ccmpbll/bitclock-redux/bitclock-fw/main/tasks/wifi_ap.c

#include "wifi_ap.h"

#include "esp_http_server.h"
#include "esp_log.h"
#include "esp_wifi.h"
#include "freertos/FreeRTOS.h"
#include "freertos/event_groups.h"
#include "tasks/wifi.h"
#include <string.h>

static const char *TAG = "wifi_ap";

#define AP_SSID "bitclock-setup"
#define AP_MAX_CONNECTIONS 4

static httpd_handle_t http_server = NULL;

// Minimal URI-decode: decodes %XX and converts + to space, in-place.
static void uri_decode(char *dst, const char *src, size_t dst_len) {
  size_t di = 0;
  for (size_t si = 0; src[si] && di + 1 < dst_len; si++) {
    if (src[si] == '%' && src[si + 1] && src[si + 2]) {
      char hex[3] = {src[si + 1], src[si + 2], '\0'};
      dst[di++] = (char)strtol(hex, NULL, 16);
      si += 2;
    } else if (src[si] == '+') {
      dst[di++] = ' ';
    } else {
      dst[di++] = src[si];
    }
  }
  dst[di] = '\0';
}

static const char *SETUP_PAGE_TEMPLATE =
    "<!DOCTYPE html>"
    "<html lang='en'>"
    "<head>"
    "<meta charset='UTF-8'>"
    "<meta name='viewport' content='width=device-width,initial-scale=1'>"
    "<title>Bitclock Wi-Fi Setup</title>"
    "<style>"
    "body{margin:0;padding:24px 16px;background:rgb(245,242,240);"
    "color:rgb(41,41,41);font-family:-apple-system,BlinkMacSystemFont,"
    "'Segoe UI',Roboto,Helvetica,Arial,sans-serif;}"
    "h1{font-size:1.4rem;font-weight:700;margin:0 0 4px;}"
    "p.sub{margin:0 0 24px;color:rgb(130,120,110);font-size:.9rem;}"
    ".card{background:#fff;border-radius:8px;padding:20px;"
    "max-width:400px;box-shadow:0 1px 4px rgba(0,0,0,.08);}"
    "label{display:block;font-size:.85rem;font-weight:600;margin-bottom:4px;}"
    "select,input{width:100%;box-sizing:border-box;padding:8px 10px;"
    "border:1px solid rgb(200,195,190);border-radius:6px;"
    "font-size:.95rem;background:#fff;color:rgb(41,41,41);margin-bottom:16px;}"
    "button{width:100%;padding:10px;border:none;border-radius:6px;"
    "background:linear-gradient(217deg,#4c6ef5,#22b8cf);"
    "color:#fff;font-size:1rem;font-weight:600;cursor:pointer;}"
    "button:active{opacity:.85;}"
    ".err{color:#c0392b;font-size:.85rem;margin-bottom:12px;display:none;}"
    "</style>"
    "</head>"
    "<body>"
    "<h1>Bitclock Wi-Fi Setup</h1>"
    "<p class='sub'>%s</p>"
    "<div class='card'>"
    "<form method='POST' action='/connect' id='f'>"
    "<label for='ssid'>Network</label>"
    "<select name='ssid' id='ssid'>%s</select>"
    "<label for='pw'>Password</label>"
    "<input type='password' name='password' id='pw' autocomplete='current-password'>"
    "<p class='err' id='err'>Please select a network.</p>"
    "<button type='submit'>Connect</button>"
    "</form>"
    "</div>"
    "<script>"
    "document.getElementById('f').onsubmit=function(){"
    "if(!document.getElementById('ssid').value){"
    "document.getElementById('err').style.display='block';return false;}"
    "return true;};"
    "</script>"
    "</body>"
    "</html>";

static const char *SUCCESS_PAGE =
    "<!DOCTYPE html>"
    "<html lang='en'>"
    "<head>"
    "<meta charset='UTF-8'>"
    "<meta name='viewport' content='width=device-width,initial-scale=1'>"
    "<title>Bitclock</title>"
    "<style>"
    "body{margin:0;padding:24px 16px;background:rgb(245,242,240);"
    "color:rgb(41,41,41);font-family:-apple-system,BlinkMacSystemFont,"
    "'Segoe UI',Roboto,Helvetica,Arial,sans-serif;text-align:center;}"
    "h1{font-size:1.4rem;font-weight:700;margin:48px 0 8px;}"
    "p{color:rgb(130,120,110);font-size:.95rem;}"
    "</style>"
    "</head>"
    "<body>"
    "<h1>Credentials saved.</h1>"
    "<p>Bitclock is restarting and will connect to your network.</p>"
    "<p>You can close this page.</p>"
    "</body>"
    "</html>";

static esp_err_t get_handler(httpd_req_t *req) {
  wifi_scan_config_t scan_cfg = {
      .ssid = NULL,
      .bssid = NULL,
      .channel = 0,
      .show_hidden = false,
  };

  esp_wifi_scan_start(&scan_cfg, true); // blocking scan

  uint16_t ap_count = 0;
  esp_wifi_scan_get_ap_num(&ap_count);
  if (ap_count > 20) {
    ap_count = 20;
  }

  wifi_ap_record_t *ap_records =
      (wifi_ap_record_t *)malloc(ap_count * sizeof(wifi_ap_record_t));
  if (!ap_records) {
    httpd_resp_send_500(req);
    return ESP_FAIL;
  }
  esp_wifi_scan_get_ap_records(&ap_count, ap_records);

  // Build <option> list — each entry: template(~27 bytes) + 2x SSID (max 32 bytes each)
  size_t opts_size = ap_count * 96 + 64;
  char *opts = (char *)malloc(opts_size);
  if (!opts) {
    free(ap_records);
    httpd_resp_send_500(req);
    return ESP_FAIL;
  }
  opts[0] = '\0';
  strlcat(opts, "<option value=''>Select a network...</option>", opts_size);
  for (uint16_t i = 0; i < ap_count; i++) {
    char opt[96];
    snprintf(opt, sizeof(opt), "<option value='%s'>%s</option>",
             (char *)ap_records[i].ssid, (char *)ap_records[i].ssid);
    strlcat(opts, opt, opts_size);
  }
  free(ap_records);

  const char *subtitle = (bool)req->user_ctx
                             ? "Could not connect to saved network."
                             : "Connect your Bitclock to Wi-Fi.";

  size_t page_size = strlen(SETUP_PAGE_TEMPLATE) + strlen(subtitle) +
                     strlen(opts) + 32;
  char *page = (char *)malloc(page_size);
  if (!page) {
    free(opts);
    httpd_resp_send_500(req);
    return ESP_FAIL;
  }
  snprintf(page, page_size, SETUP_PAGE_TEMPLATE, subtitle, opts);
  free(opts);

  httpd_resp_set_type(req, "text/html");
  httpd_resp_send(req, page, HTTPD_RESP_USE_STRLEN);
  free(page);
  return ESP_OK;
}

static esp_err_t post_handler(httpd_req_t *req) {
  char body[200] = {0};
  int received = httpd_req_recv(req, body, sizeof(body) - 1);
  if (received <= 0) {
    httpd_resp_send_500(req);
    return ESP_FAIL;
  }
  body[received] = '\0';

  // Parse ssid=...&password=...
  char raw_ssid[64] = {0};
  char raw_password[128] = {0};

  char *ssid_start = strstr(body, "ssid=");
  if (ssid_start) {
    ssid_start += 5;
    char *end = strchr(ssid_start, '&');
    size_t len = end ? (size_t)(end - ssid_start) : strlen(ssid_start);
    if (len >= sizeof(raw_ssid))
      len = sizeof(raw_ssid) - 1;
    strncpy(raw_ssid, ssid_start, len);
    raw_ssid[len] = '\0';
  }

  char *pw_start = strstr(body, "password=");
  if (pw_start) {
    pw_start += 9;
    char *end = strchr(pw_start, '&');
    size_t len = end ? (size_t)(end - pw_start) : strlen(pw_start);
    if (len >= sizeof(raw_password))
      len = sizeof(raw_password) - 1;
    strncpy(raw_password, pw_start, len);
    raw_password[len] = '\0';
  }

  char ssid[32] = {0};
  char password[64] = {0};
  uri_decode(ssid, raw_ssid, sizeof(ssid));
  uri_decode(password, raw_password, sizeof(password));

  if (ssid[0] == '\0') {
    httpd_resp_set_status(req, "400 Bad Request");
    httpd_resp_send(req, "Missing SSID", HTTPD_RESP_USE_STRLEN);
    return ESP_FAIL;
  }

  ESP_LOGI(TAG, "Received credentials for SSID: %s", ssid);

  // Save credentials via the standard wifi path so they persist across reboot
  wifi_config_t wifi_cfg = {0};
  strncpy((char *)wifi_cfg.sta.ssid, ssid, sizeof(wifi_cfg.sta.ssid));
  strncpy((char *)wifi_cfg.sta.password, password,
          sizeof(wifi_cfg.sta.password));
  esp_wifi_set_config(WIFI_IF_STA, &wifi_cfg);

  httpd_resp_set_type(req, "text/html");
  httpd_resp_send(req, SUCCESS_PAGE, HTTPD_RESP_USE_STRLEN);

  vTaskDelay(pdMS_TO_TICKS(500)); // Let the response flush
  esp_restart();

  return ESP_OK;
}

void wifi_ap_start(bool is_fallback) {
  ESP_LOGI(TAG, "Starting AP mode (fallback=%d)", is_fallback);

  // Switch to APSTA so we can still run a WiFi scan
  ESP_ERROR_CHECK(esp_wifi_set_mode(WIFI_MODE_APSTA));

  wifi_config_t ap_cfg = {
      .ap = {
          .ssid = AP_SSID,
          .ssid_len = strlen(AP_SSID),
          .channel = 1,
          .password = "",
          .max_connection = AP_MAX_CONNECTIONS,
          .authmode = WIFI_AUTH_OPEN,
      },
  };
  ESP_ERROR_CHECK(esp_wifi_set_config(WIFI_IF_AP, &ap_cfg));
  ESP_ERROR_CHECK(esp_wifi_start());

  ESP_LOGI(TAG, "AP started: SSID=%s IP=192.168.4.1", AP_SSID);

  httpd_config_t config = HTTPD_DEFAULT_CONFIG();
  config.lru_purge_enable = true;

  ESP_ERROR_CHECK(httpd_start(&http_server, &config));

  httpd_uri_t get_uri = {
      .uri = "/",
      .method = HTTP_GET,
      .handler = get_handler,
      .user_ctx = (void *)(intptr_t)is_fallback,
  };
  httpd_register_uri_handler(http_server, &get_uri);

  httpd_uri_t post_uri = {
      .uri = "/connect",
      .method = HTTP_POST,
      .handler = post_handler,
      .user_ctx = NULL,
  };
  httpd_register_uri_handler(http_server, &post_uri);
}

void wifi_ap_stop() {
  if (http_server) {
    httpd_stop(http_server);
    http_server = NULL;
  }
  esp_wifi_set_mode(WIFI_MODE_STA);
}
